TheAbsoluteMin/u-pen/assets/Case2.png

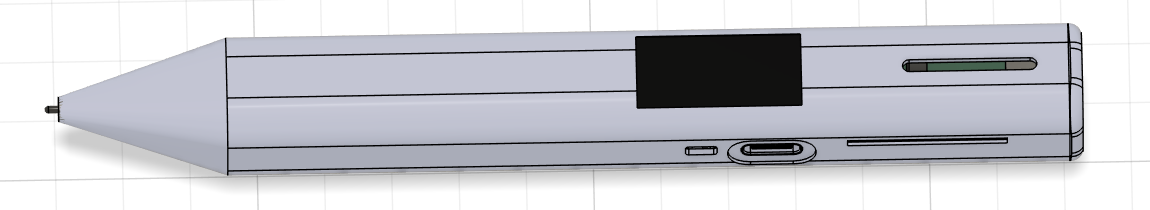
assets/Case2.png
