TheAbsoluteMin/u-pen/assets/Case3.png

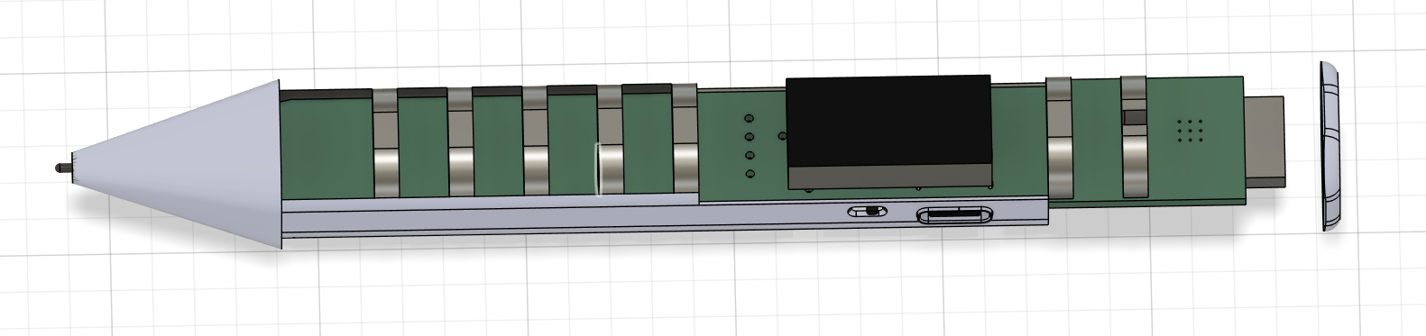
assets/Case3.png
