TheAbsoluteMin/u-pen/assets/Case4.png

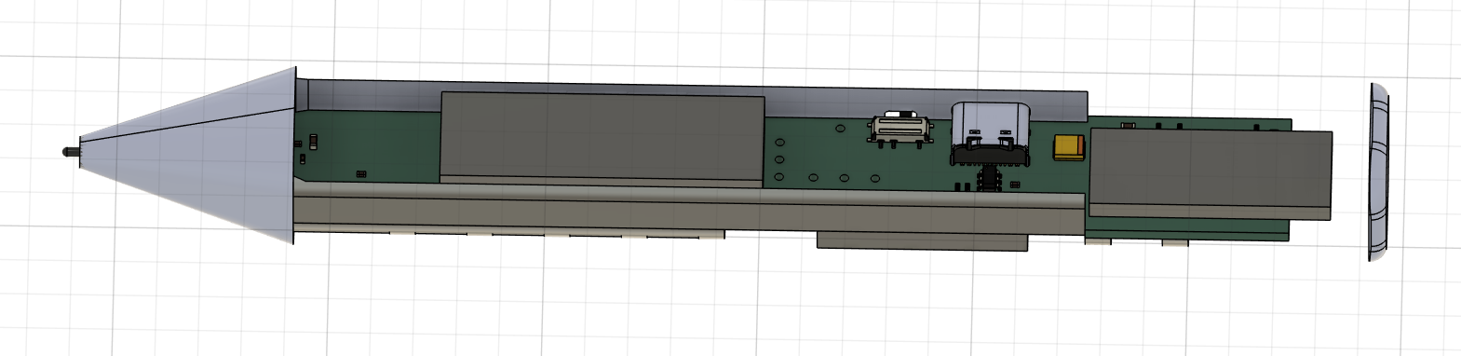
assets/Case4.png
