TheAbsoluteMin/u-pen/assets/Case5.png

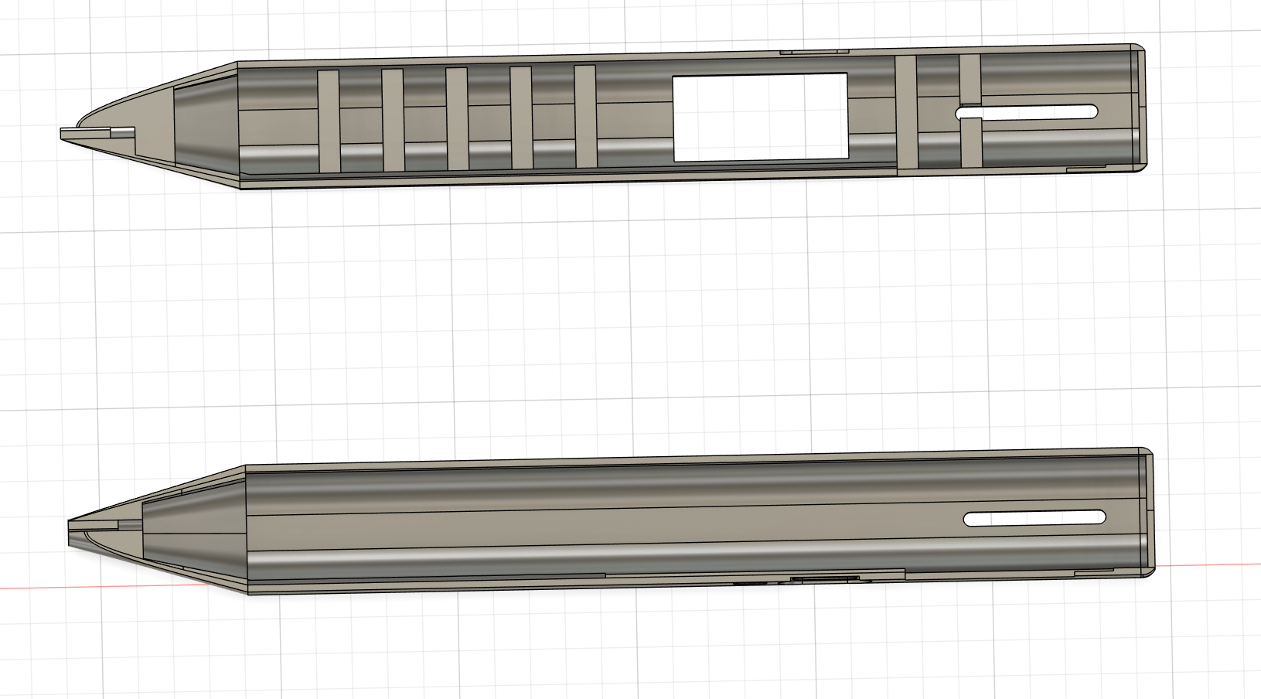
assets/Case5.png
