TheAbsoluteMin/u-pen/assets/Case6.png

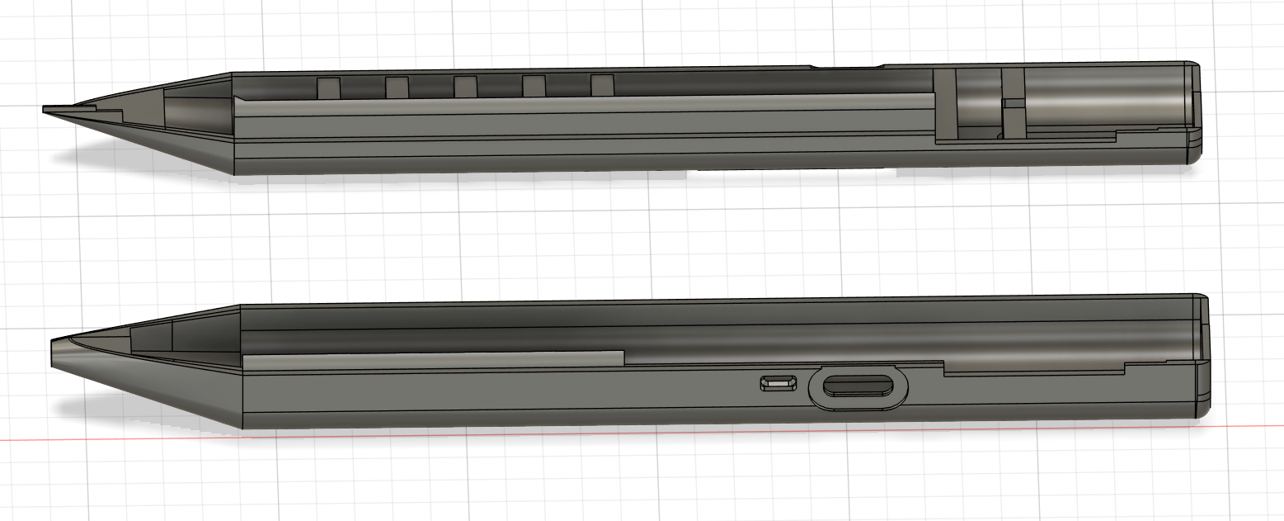
assets/Case6.png
