TheAbsoluteMin/u-pen/assets/PCB_1.png

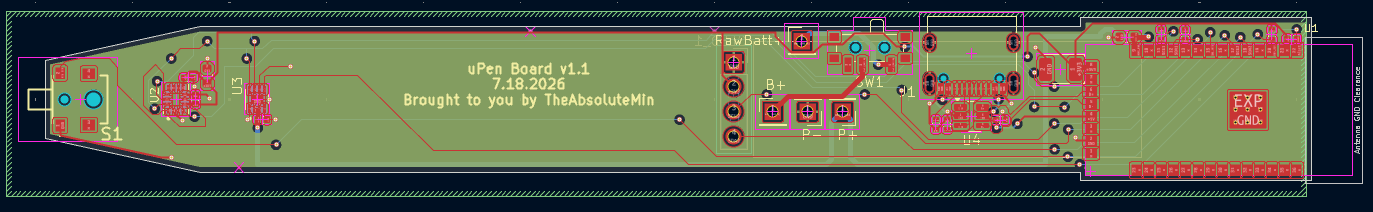
assets/PCB_1.png
