TheAbsoluteMin/u-pen/fabrication/JLCPCB/JLCPCB_Settings_1.png

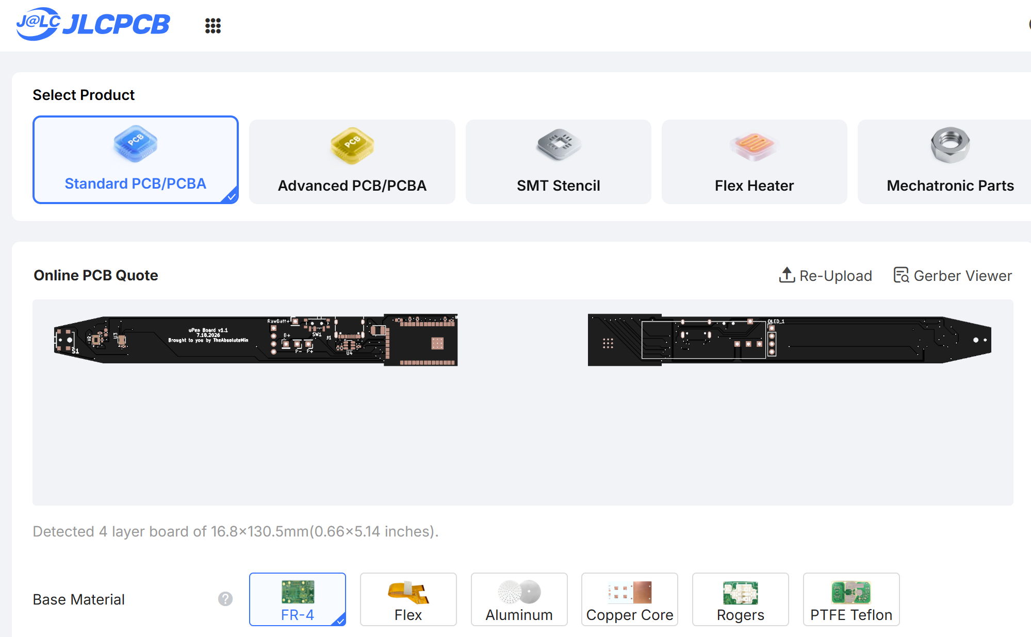
fabrication/JLCPCB/JLCPCB_Settings_1.png
