TheAbsoluteMin/u-pen/fabrication/JLCPCB/JLCPCB_Settings_2.png

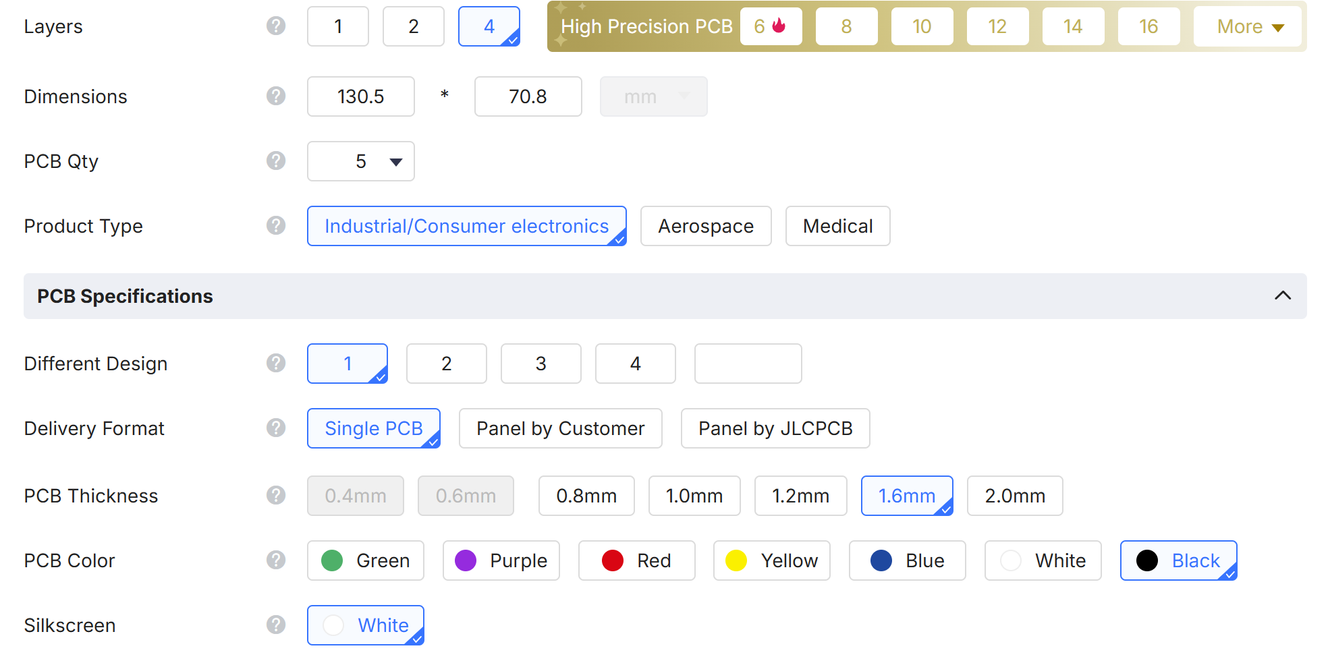
fabrication/JLCPCB/JLCPCB_Settings_2.png
