TheAbsoluteMin/u-pen/fabrication/JLCPCB/JLCPCB_Settings_3.png

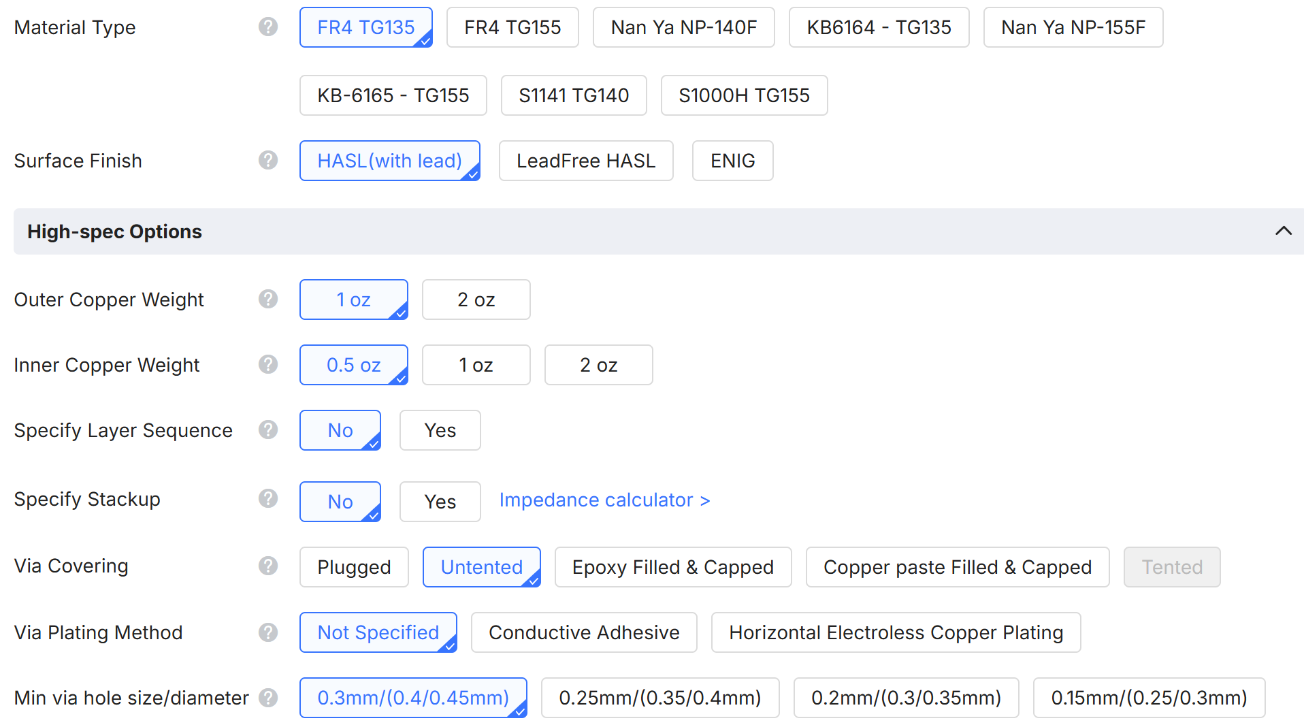
fabrication/JLCPCB/JLCPCB_Settings_3.png
