TheAbsoluteMin/u-pen/fabrication/JLCPCB/JLCPCB_Settings_4.png

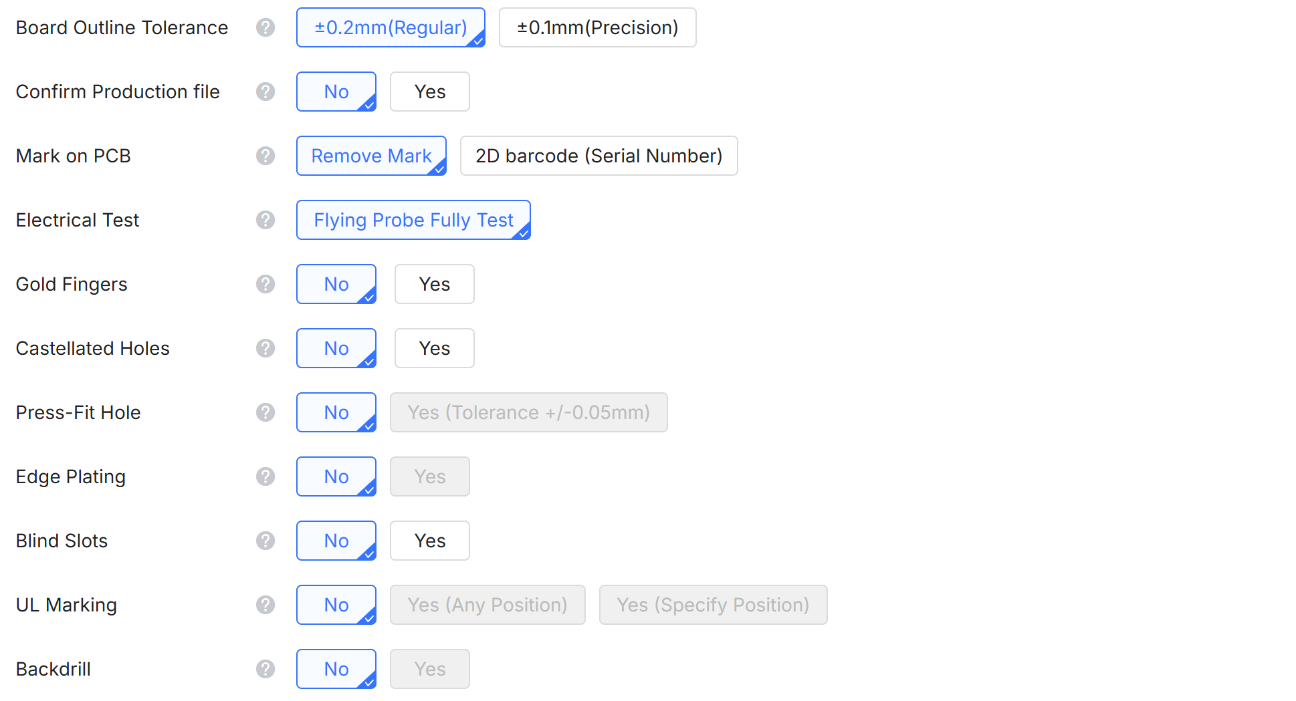
fabrication/JLCPCB/JLCPCB_Settings_4.png
