TheAbsoluteMin/u-pen/fabrication/JLCPCB/JLCPCB_Settings_5.png

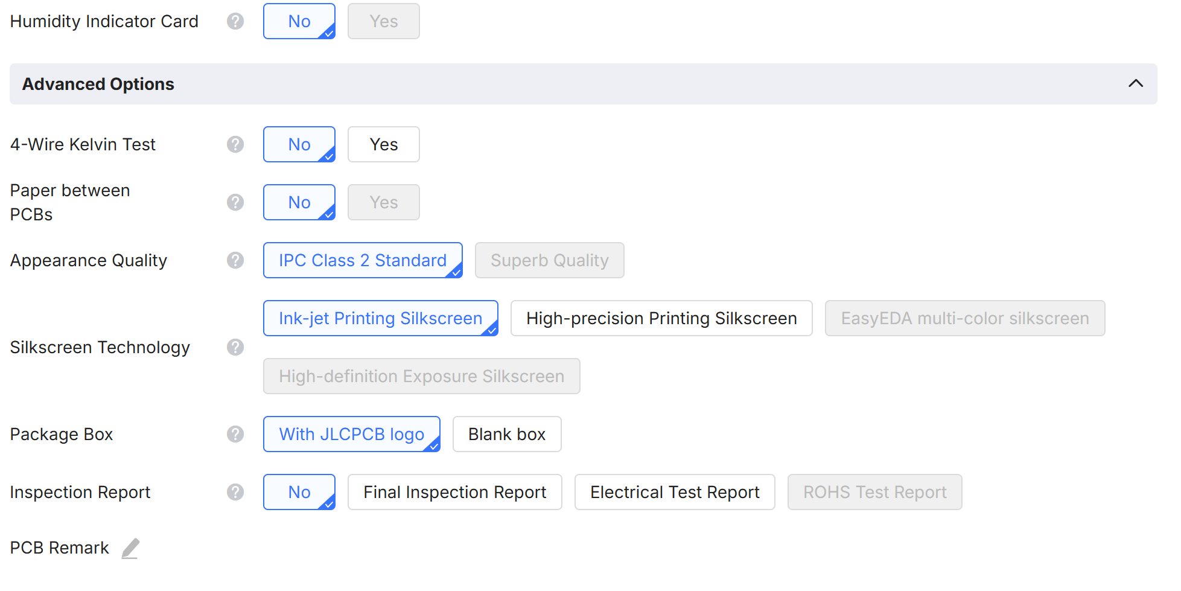
fabrication/JLCPCB/JLCPCB_Settings_5.png
