TheAbsoluteMin/u-pen/fabrication/JLCPCB/JLCPCB_Settings_6.png

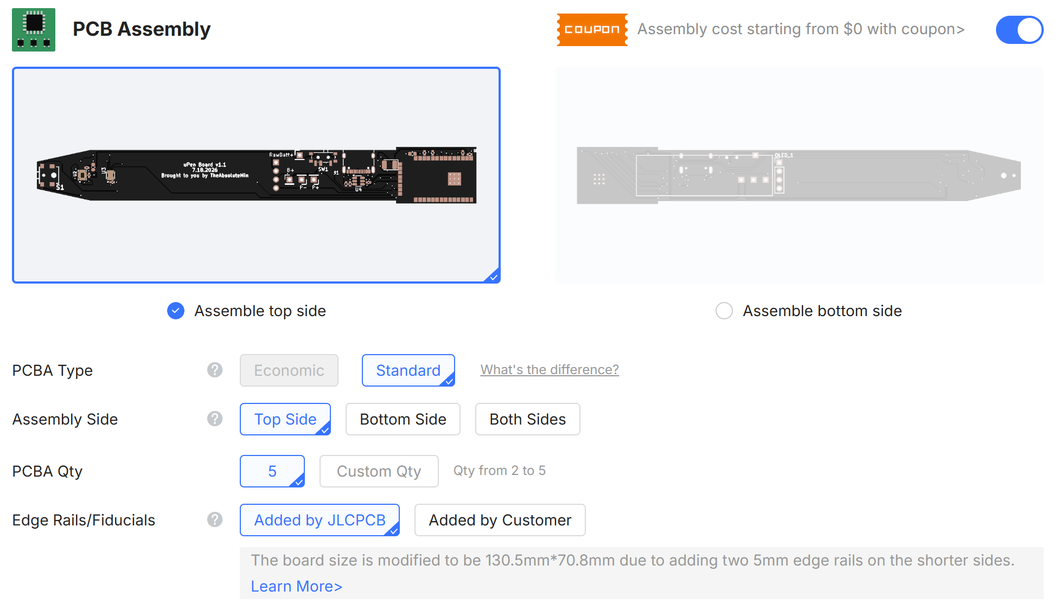
fabrication/JLCPCB/JLCPCB_Settings_6.png
