TheAbsoluteMin/u-pen/fabrication/JLCPCB/JLCPCB_Settings_7.png

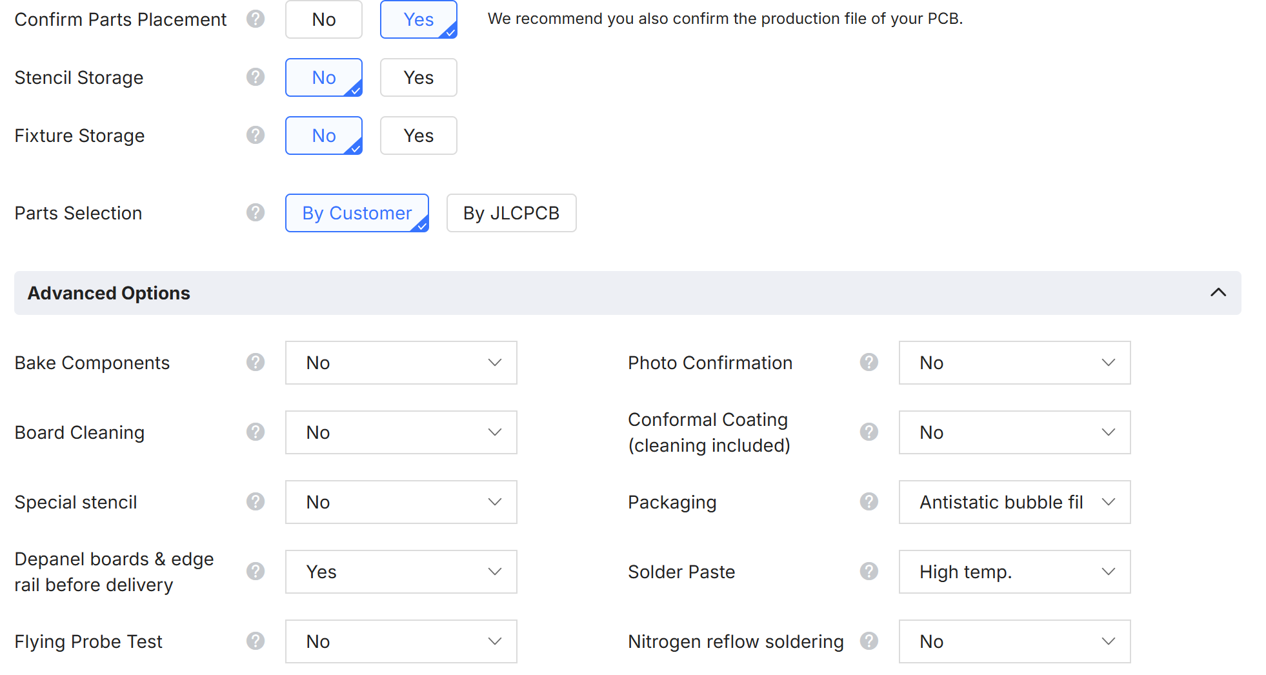
fabrication/JLCPCB/JLCPCB_Settings_7.png
