TheAbsoluteMin/u-pen/fabrication/JLCPCB/JLCPCB_Settings_9.png

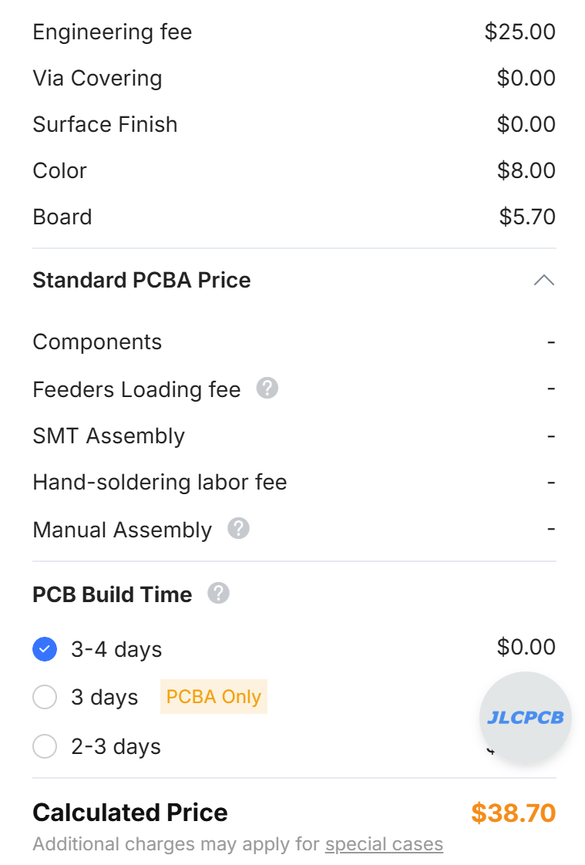
fabrication/JLCPCB/JLCPCB_Settings_9.png
